IncarboneLuca/LuCardio/doc/Schema_Memoire.pdf

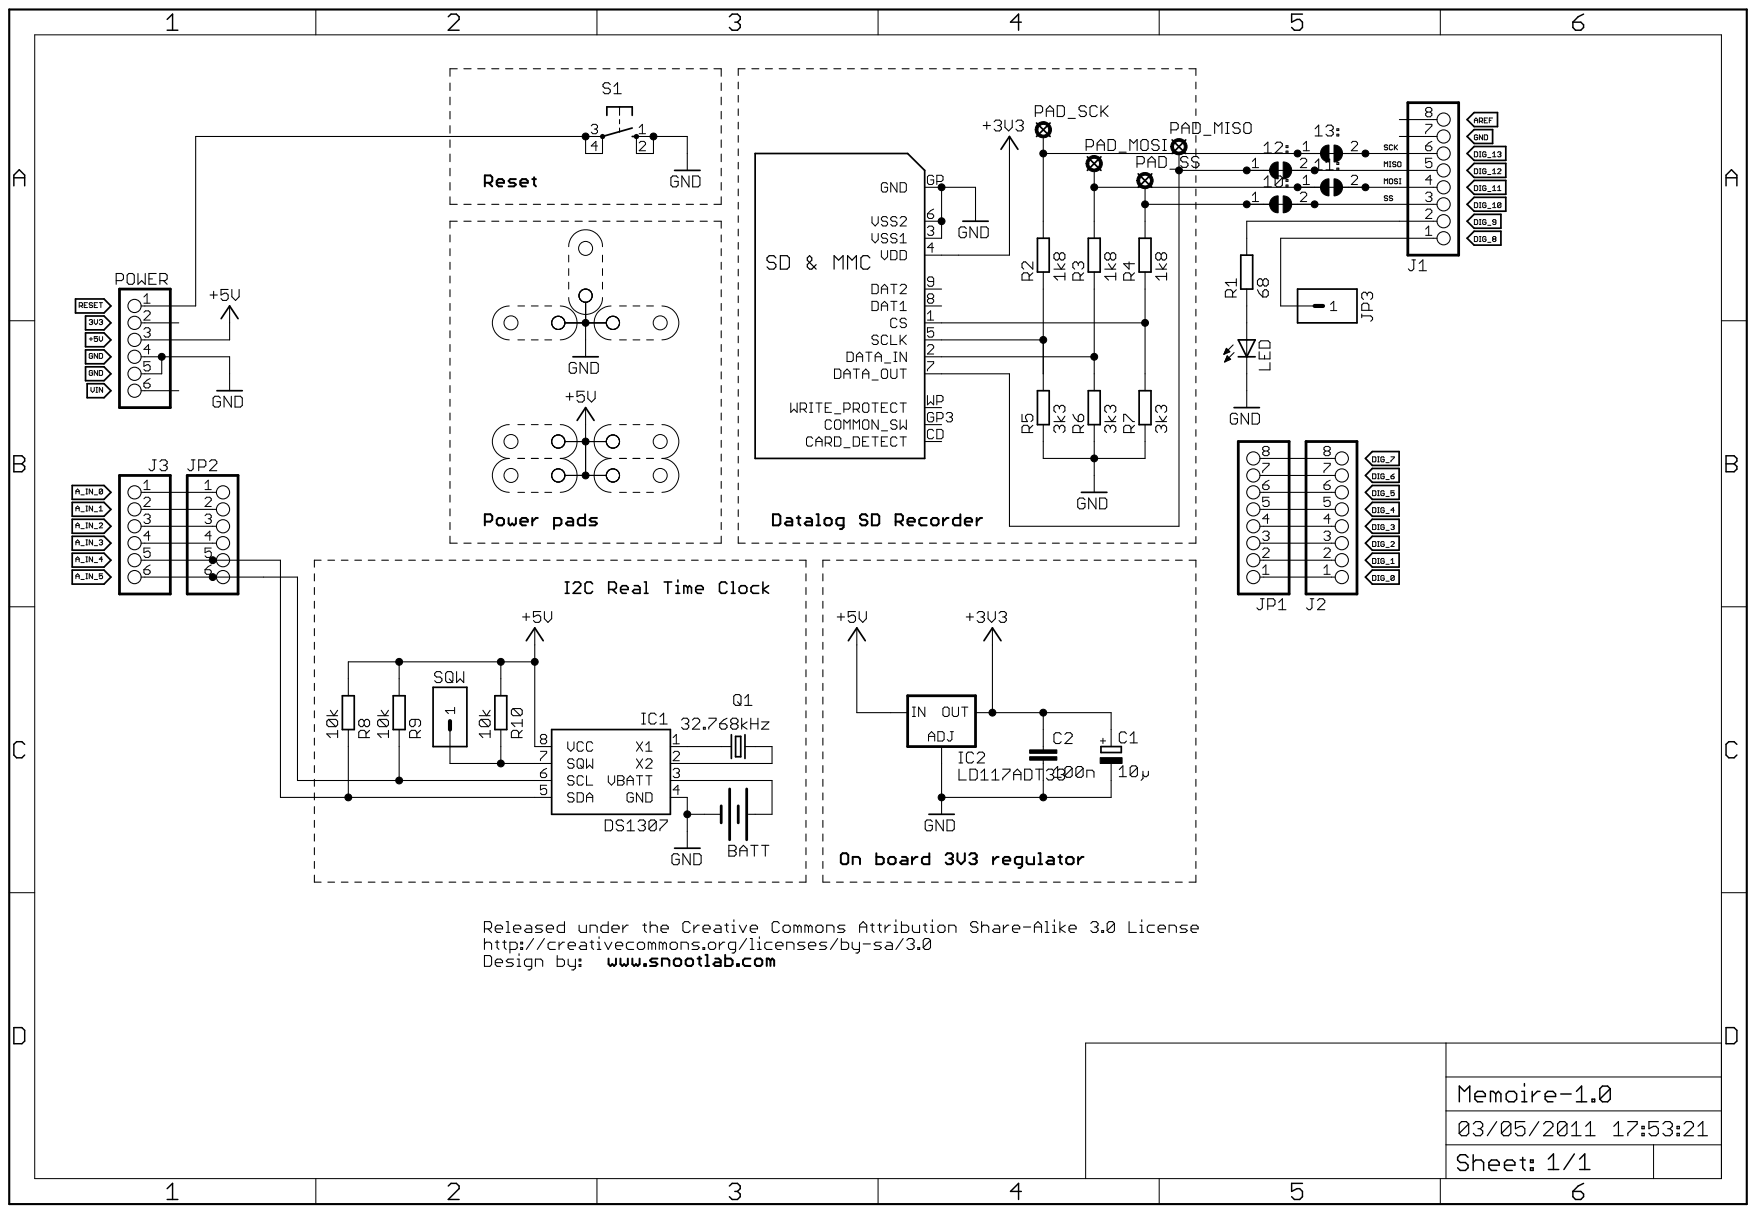
[picture p9: page 1]
