IncarboneLuca/LuCardio/sch/LuCardio.sch

## KiCad design sch/LuCardio.sch (2021-09-26)

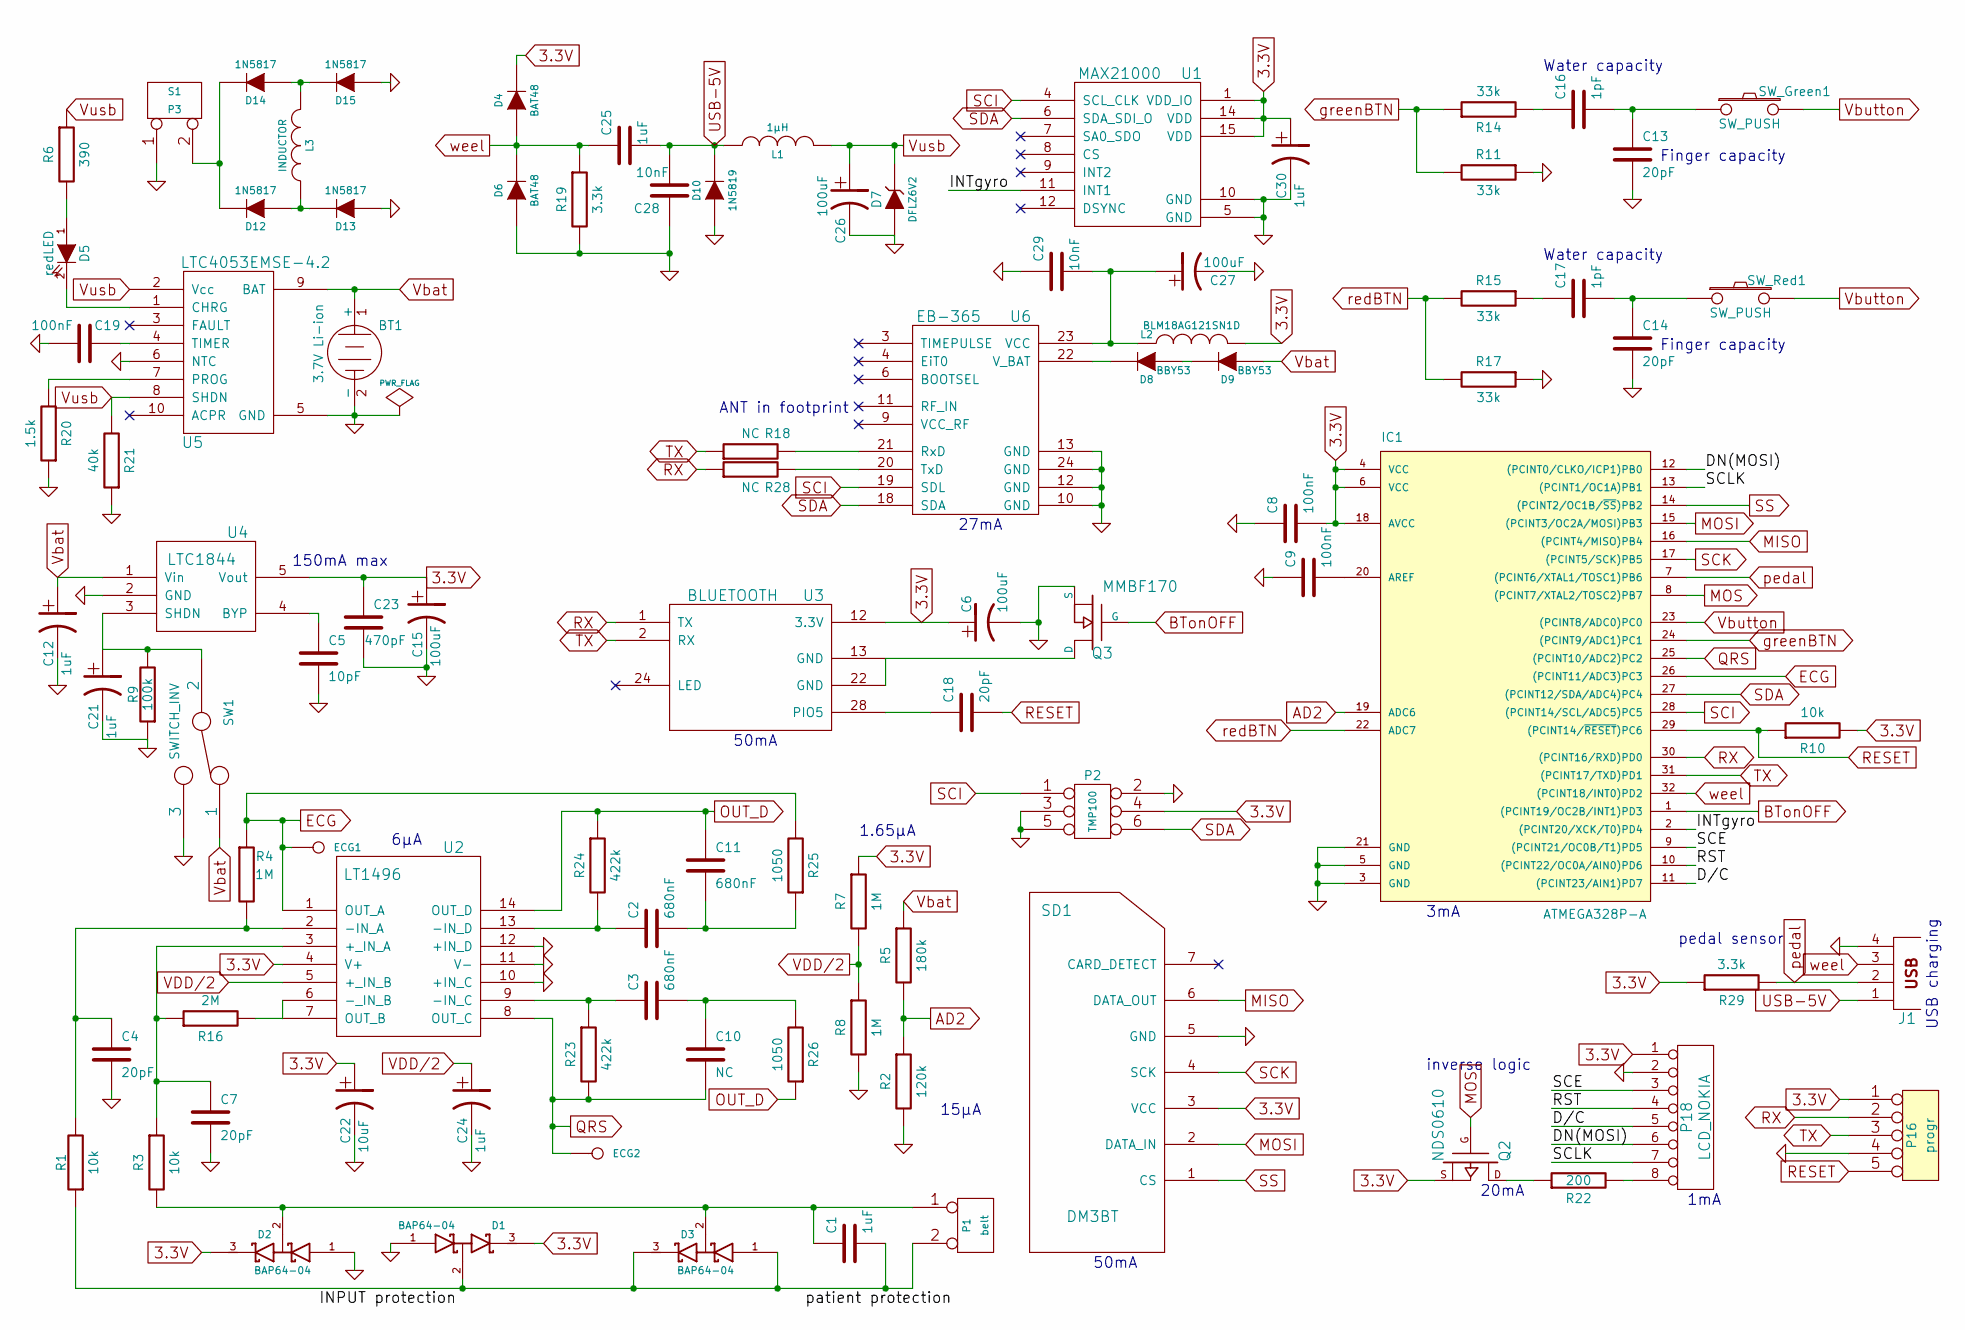
[picture p10: schematic LuCardio.sch]

Parts:
BT1: 3.7V Li-ion
C1, C21, C24, C30: 1uF
C2, C3, C11: 680nF
C4, C7: 20pF
C5: 10pF
C6, C15, C26, C27: 100uF
C8, C9, C19: 100nF
C10: NC
C12: 1uF; 0805
C13, C14, C18: 20pF
C16, C17: 1pF
C22: 10uF
C23: 470pF
C25: 1uF
C28, C29: 10nF
D1, D2, D3: BAP64-04
D4, D6: BAT48
D5: redLED
D7: DFLZ6V2
D8, D9: BBY53
D10: 1N5819
D12, D13, D14, D15: 1N5817
ECG1, ECG2: 1
IC1: ATMEGA328P-A; TQFP32
J1: USB_2; USBmicroB
L1: 1µH
L2: BLM18AG121SN1D
L3: INDUCTOR
P1: belt
P2: TMP100
P3: S1
P16: progr
P18: LCD_NOKIA
Q2: NDS0610
Q3: MMBF170
R1, R3, R10: 10k
R2: 120k
R4, R7, R8: 1M
R5: 180k
R6: 390
R9: 100k
R11, R14, R15, R17: 33k
R16: 2M
R18, R28: NC
R19, R29: 3.3k
R20: 1.5k
R21: 40k
R22: 200
R23, R24: 422k
R25, R26: 1050
SD1: DM3BT
SW1: SWITCH_INV
SW_Green1: SW_PUSH
SW_Red1: SW_PUSH
U1: MAX21000
U2: LT1496
U3: BLUETOOTH
U4: LTC1844
U5: LTC4053EMSE-4.2
U6: EB-365

Connections:
3.3V: C6.1, C8.2, C15.1, C22.1, C23.1, C30.1, D1.3 (cathode), D2.3 (cathode), D4.2 (K), IC1.4 (VCC), IC1.6 (VCC), IC1.18 (AVCC), L2.2, P2.4, P16.1, P18.1, Q2.S, R7.1, R10.2, R29.1, SD1.3 (VCC), U1.1 (VDD_IO), U1.14 (VDD), U1.15 (VDD), U2.4 (V+), U3.12 (3.3V), U4.5 (Vout)
AD2: IC1.19 (ADC6), R2.1, R5.2
BTonOFF: IC1.1 ((PCINT19/OC2B/INT1)PD3), Q3.G
D/C: IC1.11 ((PCINT23/AIN1)PD7), P18.5
DN(MOSI): IC1.12 ((PCINT0/CLKO/ICP1)PB0), P18.6
ECG: ECG1.1, IC1.26 ((PCINT11/ADC3)PC3), R4.1, R25.2, U2.1 (OUT_A)
GND: BT1.2 (-), C4.2, C5.2, C6.2, C7.2, C8.1, C9.1, C12.2, C13.2, C14.2, C15.2, C19.2, C21.2, C22.2, C23.2, C24.2, C26.2, C27.2, C28.1, C29.1, C30.2, D1.1 (Anode), D2.1 (Anode), D6.1 (A), D7.1 (A), D10.1 (A), D13.1 (A), D15.1 (A), IC1.3 (GND), IC1.5 (GND), IC1.21 (GND), J1.4, P2.2, P2.3, P2.5, P3.1, P16.4, P18.2, Q3.S, R2.2, R8.2, R9.1, R11.1, R17.1, R19.2, R20.1, R21.1, SD1.5 (GND), SW1.3, U1.5 (GND), U1.10 (GND), U2.10 (+IN_C), U2.11 (V-), U2.12 (+IN_D), U4.2 (GND), U5.5 (GND), U5.6 (NTC), U6.10 (GND), U6.12 (GND), U6.13 (GND), U6.24 (GND)
INTgyro: IC1.2 ((PCINT20/XCK/T0)PD4), U1.11 (INT1)
MISO: IC1.16 ((PCINT4/MISO)PB4), SD1.6 (DATA_OUT)
MOS: IC1.8 ((PCINT7/XTAL2/TOSC2)PB7), Q2.G
MOSI: IC1.15 ((PCINT3/OC2A/MOSI)PB3), SD1.2 (DATA_IN)
unnamed: C1.1, D2.2 (AK), D3.2 (AK), P1.1, R3.2
unnamed: C1.2, D1.2 (AK), D3.1 (Anode), D3.3 (cathode), P1.2 (PM), R1.1
unnamed: C2.1, R24.2, U2.13 (-IN_D)
unnamed: C3.1, R23.1, U2.9 (-IN_C)
unnamed: C4.1, R1.2, R4.2, U2.2 (-IN_A)
unnamed: C5.1, U4.4 (BYP)
unnamed: C7.1, R3.1, R16.1, U2.3 (+_IN_A)
unnamed: C9.2, IC1.20 (AREF)
unnamed: C3.2, C10.1, R26.2
unnamed: C2.2, C11.2, R25.1
unnamed: C13.1, C16.2, SW_Green1.1
unnamed: C14.1, C17.2, SW_Red1.1
unnamed: C16.1, R14.2
unnamed: C17.1, R15.1
unnamed: C18.1, U3.28 (PIO5)
unnamed: C19.1, U5.4 (TIMER)
unnamed: C21.1, R9.2, SW1.2, U4.3 (SHDN)
unnamed: C27.1, C29.2, L2.1, U6.23 (VCC)
unnamed: D5.1 (A), R6.2
unnamed: D5.2 (K), U5.1 (CHRG)
unnamed: D8.1 (A), D9.2 (K)
unnamed: D8.2 (K), U6.22 (V_BAT)
unnamed: D12.1 (A), D13.2 (K), L3.1
unnamed: D12.2 (K), D14.2 (K), P3.2 (PM)
unnamed: D14.1 (A), D15.2 (K), L3.2
unnamed: P18.8, R22.2
unnamed: Q2.D, R22.1
unnamed: Q3.D, U3.13 (GND), U3.22 (GND)
unnamed: R16.2, U2.6 (-_IN_B), U2.7 (OUT_B)
unnamed: R18.2, U6.21 (RxD)
unnamed: R20.2, U5.7 (PROG)
unnamed: R28.2, U6.20 (TxD)
OUT_D: C11.1, R24.1, R26.1, U2.14 (OUT_D)
QRS: C10.2, ECG2.1, IC1.25 ((PCINT10/ADC2)PC2), R23.2, U2.8 (OUT_C)
RESET: C18.2, IC1.29 ((PCINT14/~RESET~)PC6), P16.5, R10.1
RST: IC1.10 ((PCINT22/OC0A/AIN0)PD6), P18.4
RX: IC1.30 ((PCINT16/RXD)PD0), P16.2, R28.1, U3.1 (TX)
SCE: IC1.9 ((PCINT21/OC0B/T1)PD5), P18.3
SCI: IC1.28 ((PCINT14/SCL/ADC5)PC5), P2.1, U1.4 (SCL_CLK), U6.19 (SDL)
SCK: IC1.17 ((PCINT5/SCK)PB5), SD1.4 (SCK)
SCLK: IC1.13 ((PCINT1/OC1A)PB1), P18.7
SDA: IC1.27 ((PCINT12/SDA/ADC4)PC4), P2.6, U1.6 (SDA_SDI_O), U6.18 (SDA)
SS: IC1.14 ((PCINT2/OC1B/~SS~)PB2), SD1.1 (CS)
TX: IC1.31 ((PCINT17/TXD)PD1), P16.3, R18.1, U3.2 (RX)
USB-5V: C25.2, C28.2, D10.2 (K), J1.1, L1.1
VDD/2: C24.1, R7.2, R8.1, U2.5 (+_IN_B)
Vbat: BT1.1 (+), C12.1, D9.1 (A), R5.1, SW1.1, U4.1 (Vin), U5.9 (BAT)
Vbutton: IC1.23 ((PCINT8/ADC0)PC0), SW_Green1.2, SW_Red1.2
Vusb: C26.1, D7.2 (K), L1.2, R6.1, R21.2, U5.2 (Vcc), U5.8 (SHDN)
greenBTN: IC1.24 ((PCINT9/ADC1)PC1), R11.2, R14.1
pedal: IC1.7 ((PCINT6/XTAL1/TOSC1)PB6), J1.2, R29.2
redBTN: IC1.22 (ADC7), R15.2, R17.2
weel: C25.1, D4.1 (A), D6.2 (K), IC1.32 ((PCINT18/INT0)PD2), J1.3, R19.1

Notes on the sheet:
20mA
USB charging
pedal sensor
150mA max
50mA
1mA
6µA
27mA
3mA
1.65µA
15µA
ANT in footprint
inverse logic
Water capacity
Finger capacity
